icfaust/IPPIoT/code/jsonparse.c

/*
 * Copyright (c) 2011-2012, Swedish Institute of Computer Science.
 * All rights reserved.
 *
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
 * This file is part of the Contiki operating system.
 */
#include "osapi.h"

#include "jsonparse.h"
#include <stdlib.h>

/*--------------------------------------------------------------------*/
static int ICACHE_FLASH_ATTR 
push(struct jsonparse_state *state, char c)
{
  state->stack[state->depth] = c;
  state->depth++;
  state->vtype = 0;
  return state->depth < JSONPARSE_MAX_DEPTH;
}
/*--------------------------------------------------------------------*/
static void ICACHE_FLASH_ATTR 
modify(struct jsonparse_state *state, char c)
{
  if(state->depth > 0) {
    state->stack[state->depth - 1] = c;
  }
}
/*--------------------------------------------------------------------*/
static char ICACHE_FLASH_ATTR 
pop(struct jsonparse_state *state)
{
  if(state->depth == 0) {
    return JSON_TYPE_ERROR;
  }
  state->depth--;
  state->vtype = state->stack[state->depth];
  return state->stack[state->depth];
}
/*--------------------------------------------------------------------*/
/* will pass by the value and store the start and length of the value for
   atomic types */
/*--------------------------------------------------------------------*/
static char ICACHE_FLASH_ATTR
atomic(struct jsonparse_state *state, char type)
{
  char c;
  const char *str;
  int len;

  state->vstart = state->pos;
  if(type == JSON_TYPE_STRING || type == JSON_TYPE_PAIR_NAME) {
    while((c = state->json[state->pos++]) && c != '"') {
      if(c == '\\') {
        state->pos++;           /* skip current char */
      }
    }
    if (c != '"') {
      state->error = JSON_ERROR_SYNTAX;
      return JSON_TYPE_ERROR;
    }
    state->vlen = state->pos - state->vstart - 1;
  } else if(type == JSON_TYPE_NUMBER) {
    do {
      c = state->json[state->pos];
      if((c < '0' || c > '9') && c != '.') {
        c = 0;
      } else {
        state->pos++;
      }
    } while(c);
    /* need to back one step since first char is already gone */
    state->vstart--;
    state->vlen = state->pos - state->vstart;
  } else if(type == JSON_TYPE_NULL || type == JSON_TYPE_TRUE || type == JSON_TYPE_FALSE) {
    state->vstart--;
    switch (type) {
    case JSON_TYPE_NULL:  str = "null";  break;
    case JSON_TYPE_TRUE:  str = "true";  break;
    case JSON_TYPE_FALSE: str = "false"; break;
    default:              str = "";      break;
    }

    while ((c = state->json[state->pos]) && c != ' ' && c != ',' && c != ']' && c != '}') {
      state->pos++;
    }

    state->vlen = state->pos - state->vstart;
    len = strlen(str);
    len = state->vlen > len ? state->vlen : len;

    if (strncmp(str, &state->json[state->vstart], len) != 0) {
      state->error = JSON_ERROR_SYNTAX;
      return JSON_TYPE_ERROR;
    }
  }

  state->vtype = type;
  return state->vtype;
}
/*--------------------------------------------------------------------*/
static void ICACHE_FLASH_ATTR
skip_ws(struct jsonparse_state *state)
{
  char c;

  while(state->pos < state->len &&
        ((c = state->json[state->pos]) == ' ' || c == '\n')) {
    state->pos++;
  }
}
/*--------------------------------------------------------------------*/
static int ICACHE_FLASH_ATTR
is_atomic(struct jsonparse_state *state)
{
  char v = state->vtype;
  if(v == 'N' || v == '"' || v == '0' || v == 'n' || v == 't' || v == 'f') {
    return 1;
  } else {
    return 0;
  }
}
/*--------------------------------------------------------------------*/
void ICACHE_FLASH_ATTR
jsonparse_setup(struct jsonparse_state *state, const char *json, int len)
{
  state->json = json;
  state->len = len;
  state->pos = 0;
  state->depth = 0;
  state->error = 0;
  state->vtype = 0;
  state->stack[0] = 0;
}
/*--------------------------------------------------------------------*/
int ICACHE_FLASH_ATTR
jsonparse_next(struct jsonparse_state *state)
{
  char c;
  char s;
  char v;

  skip_ws(state);
  c = state->json[state->pos];
  s = jsonparse_get_type(state);
  v = state->vtype;
  state->pos++;

  switch(c) {
  case '{':
    if((s == 0 && v == 0) || s == '[' || s == ':') {
      push(state, c);
    } else {
      state->error = JSON_ERROR_UNEXPECTED_OBJECT;
      return JSON_TYPE_ERROR;
    }
    return c;
  case '}':
    if((s == ':' && v != ',' && v != 0 ) || (s == '{' && v == 0)) {
      pop(state);
    } else {
      state->error = JSON_ERROR_UNEXPECTED_END_OF_ARRAY;
      return JSON_TYPE_ERROR;
    }
    return c;
  case ']':
    if(s == '[' && v != ',') {
      pop(state);
    } else {
      state->error = JSON_ERROR_UNEXPECTED_END_OF_ARRAY;
      return JSON_TYPE_ERROR;
    }
    return c;
  case ':':
    if(s == '{' && v == 'N') {
      modify(state, ':');
      state->vtype = 0;
    } else {
      state->error = JSON_ERROR_SYNTAX;
      return JSON_TYPE_ERROR;
    }
    return jsonparse_next(state);
  case ',':
    if(s == ':' && v != 0) {
      modify(state, '{');
      state->vtype = c;
    } else if(s == '[') {
      state->vtype = c;
    } else {
      state->error = JSON_ERROR_SYNTAX;
      return JSON_TYPE_ERROR;
    }
    return c;
  case '"':
    if((s == 0 && v == 0) || s == '{' || s == '[' || s == ':') {
      return atomic(state, c = (s == '{' ? JSON_TYPE_PAIR_NAME : c));
    } else {
      state->error = JSON_ERROR_UNEXPECTED_STRING;
      return JSON_TYPE_ERROR;
    }
    return c;
  case '[':
    if((s == 0 && v == 0) || s == '[' || s == ':') {
      push(state, c);
    } else {
      state->error = JSON_ERROR_UNEXPECTED_ARRAY;
      return JSON_TYPE_ERROR;
    }
    return c;
  case 0:
    if(v == 0 || state->depth > 0) {
      state->error = JSON_ERROR_SYNTAX;
    }
    return JSON_TYPE_ERROR;
  default:
    if(s == 0 || s == ':' || s == '[') {
      if (v != 0 && v != ',') {
        state->error = JSON_ERROR_SYNTAX;
        return JSON_TYPE_ERROR;
      }
      if(c == '-' || (c <= '9' && c >= '0')) {
        return atomic(state, JSON_TYPE_NUMBER);
      } else if(c == 'n') {
        return atomic(state, JSON_TYPE_NULL);
      } else if(c == 't') {
        return atomic(state, JSON_TYPE_TRUE);
      } else if(c == 'f') {
        return atomic(state, JSON_TYPE_FALSE);
      } else {
        state->error = JSON_ERROR_SYNTAX;
        return JSON_TYPE_ERROR;
      }
    } else if(s == '{') {
      state->error = JSON_ERROR_SYNTAX;
      return JSON_TYPE_ERROR;
    }
  }
  return 0;
}
/*--------------------------------------------------------------------*/
/* get the json value of the current position
 * works only on "atomic" values such as string, number, null, false, true
 */
/*--------------------------------------------------------------------*/
int ICACHE_FLASH_ATTR
jsonparse_copy_value(struct jsonparse_state *state, char *str, int size)
{
  int i, o;
  char c;

  if(!is_atomic(state)) {
    return 0;
  }
  for(i = 0, o = 0; i < state->vlen && o < size - 1; i++) {
    c = state->json[state->vstart + i];
    if(c == '\\') {
      i++;
      switch(state->json[state->vstart + i]) {
      case '"':  str[o++] = '"';  break;
      case '\\': str[o++] = '\\'; break;
      case '/':  str[o++] = '/';  break;
      case 'b':  str[o++] = '\b'; break;
      case 'f':  str[o++] = '\f'; break;
      case 'n':  str[o++] = '\n'; break;
      case 'r':  str[o++] = '\r'; break;
      case 't':  str[o++] = '\t'; break;
      }
      continue;
    }
    str[o++] = c;
  }
  str[o] = 0;
  return state->vtype;
}
/*--------------------------------------------------------------------*/
int ICACHE_FLASH_ATTR
jsonparse_get_value_as_int(struct jsonparse_state *state)
{
  if(state->vtype != JSON_TYPE_NUMBER) {
    return 0;
  }
  return atoi(&state->json[state->vstart]);
}
/*--------------------------------------------------------------------*/
long ICACHE_FLASH_ATTR
jsonparse_get_value_as_long(struct jsonparse_state *state)
{
  if(state->vtype != JSON_TYPE_NUMBER) {
    return 0;
  }
  return atol(&state->json[state->vstart]);
}
/*--------------------------------------------------------------------*/
int ICACHE_FLASH_ATTR
jsonparse_get_len(struct jsonparse_state *state)
{
  return state->vlen;
}
/*--------------------------------------------------------------------*/
int ICACHE_FLASH_ATTR
jsonparse_get_type(struct jsonparse_state *state)
{
  if(state->depth == 0) {
    return 0;
  }
  return state->stack[state->depth - 1];
}
/*--------------------------------------------------------------------*/
int ICACHE_FLASH_ATTR
jsonparse_has_next(struct jsonparse_state *state)
{
  return state->pos < state->len;
}
/*--------------------------------------------------------------------*/
